dark-node/Dosimeter-Radiometer.-Promin-1.-DIY-Project.-Based-on-the-ESP32-C3-mini-and-SI-22G/media/photos-build/build-4.jpg

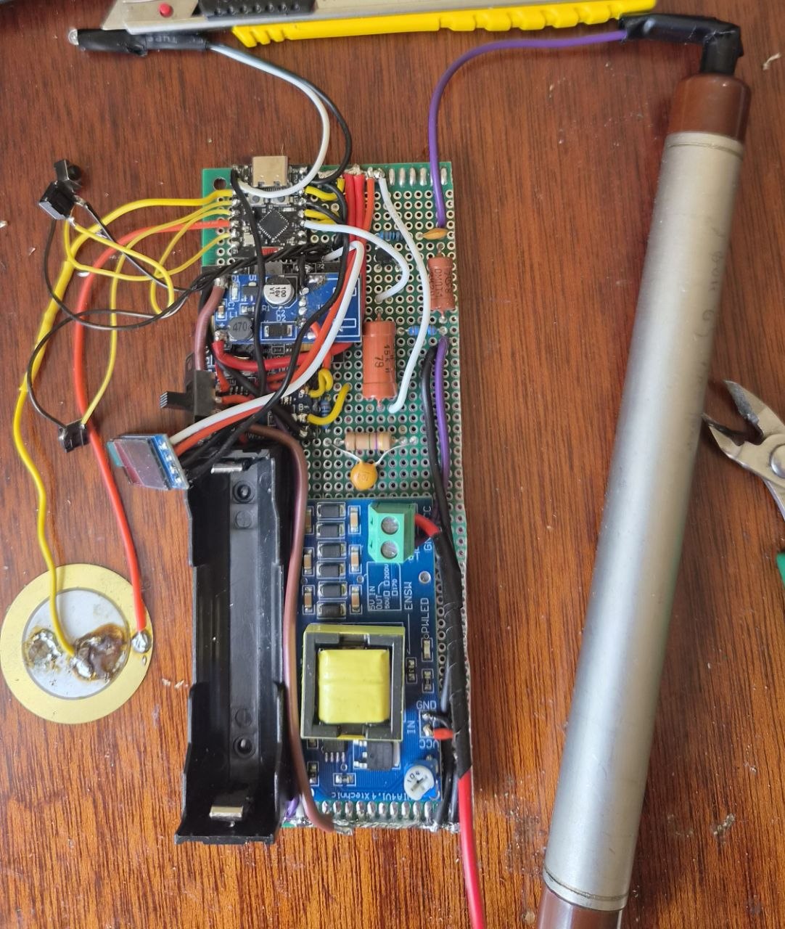
media/photos-build/build-4.jpg
