dark-node/Dosimeter-Radiometer.-Promin-1.-DIY-Project.-Based-on-the-ESP32-C3-mini-and-SI-22G/hardware/schematics/promin1-connections.asc

C_DET: cap; 470n
D_LED: LED
PZ: cap; Piezo
Q1: npn; BC547B
R_BALLAST: res; 10Meg
R_BASE: res; 4.7Meg
R_BAT_H: res; 10Meg
R_BAT_L: res; 4.7Meg
R_CATH: res; 10k
R_COLL: res; 15k
R_LED: res; 330
R_SER: res; 50k
SW_CNT: sw
SW_CPM: sw
SW_USV: sw
TUBE: diode; SI-22G
V3V3: voltage; 3.3
VBAT: voltage; 4.2
VHV: voltage; 405
Named nets: VBAT, 0, HV405, 3V3, GPIO2, GPIO3, GPIO6, GPIO7, GPIO10, GPIO8, GPIO9, GPIO20, GPIO4, GPIO5
Same net name = same wire. Documentation, not for simulation.
POWER
Battery 3.7-4.2V
HV module ~405V
3V3 (ESP out)
HV + DETECTOR
ANODE
DET
BASE
BATTERY ADC (GPIO3)
INDICATORS
D_LED = LED
PIEZO push-pull (GPIO7 / GPIO10)
Buttons to GND (active LOW, MCU pull-up)
GPIO8=CPM  GPIO9=uSv/h  GPIO20=count
OLED SSD1306 128x32
VCC = 3V3 (NOT 5V)
GND
SDA = GPIO4
SCL = GPIO5
ESP32-C3 Super Mini
GPIO2  Geiger IN (ISR)
GPIO3  Battery ADC
GPIO4  OLED SDA
GPIO5  OLED SCL
GPIO6  LED
GPIO7  Piezo center
GPIO8  Button CPM
GPIO9  Button uSv/h
GPIO10 Piezo ring
GPIO20 Button count
3V3 out
5V / VIN (battery)
GND
WARNINGS
1. Never USB + external battery together
2. Do not press GPIO8/GPIO9 during power-on (strapping)
3. Calibration: 800 CPM per uSv/h @ HV 405V, ballast 10M
4. Measure 405V between HV+ and GND on module terminals
5. C_DET 470nF, R_SER 50k, R_BASE 4.7M, no diodes on GPIO2
PROMIN-1 - assembly wiring reference
