dark-node/Dosimeter-Radiometer.-Promin-1.-DIY-Project.-Based-on-the-ESP32-C3-mini-and-SI-22G/hardware/schematics/si22g-simulation.asc

1N4148: diode
BC547: npn
C1: cap; 1nF
Control_SW: voltage; PULSE(0 5 0 1u 1u 100u 2)
CTube: cap; 5pF
R1: res; 100k
R2: res; 100k
R3: res; 10k
S1: sw
SW: res; 4.7Meg
V1: voltage; 400
V2: voltage; 3.3
Named nets: 0, HV, PulseOut, GPIO
.model SW SW(Ron=1 Roff=1G Vt=2)
.tran 0 6 0 1u
